richardhawthorn/piZero-Hub/images/image3.jpg

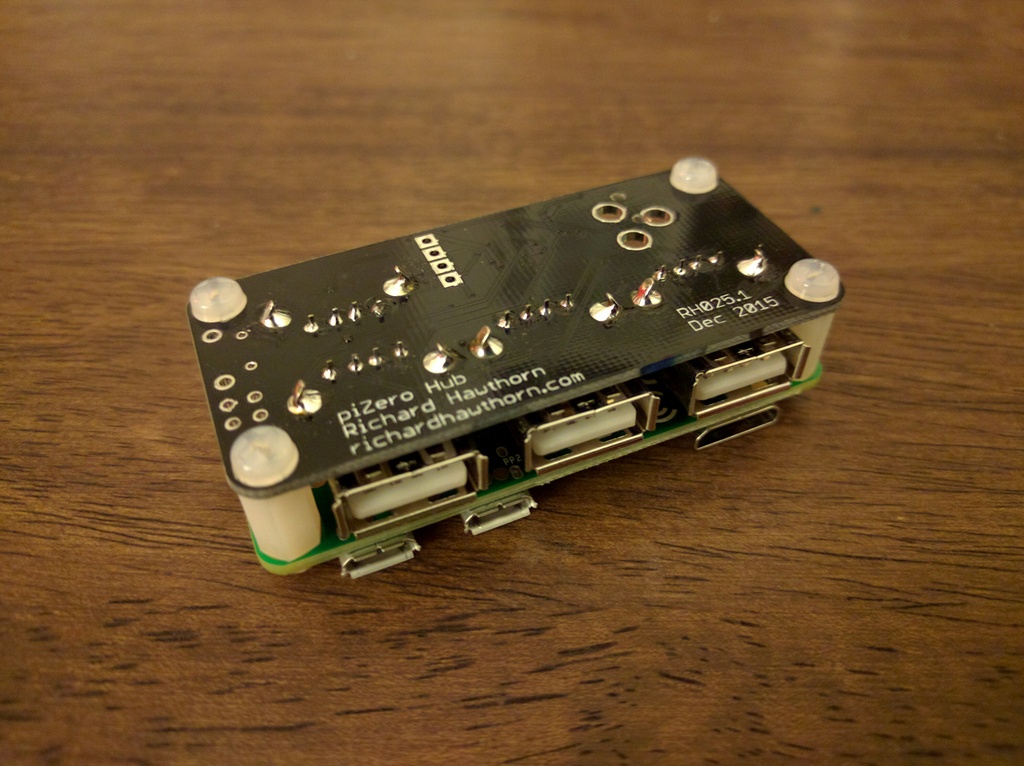
images/image3.jpg
