richardhawthorn/piZero-Hub/images/image4.jpg

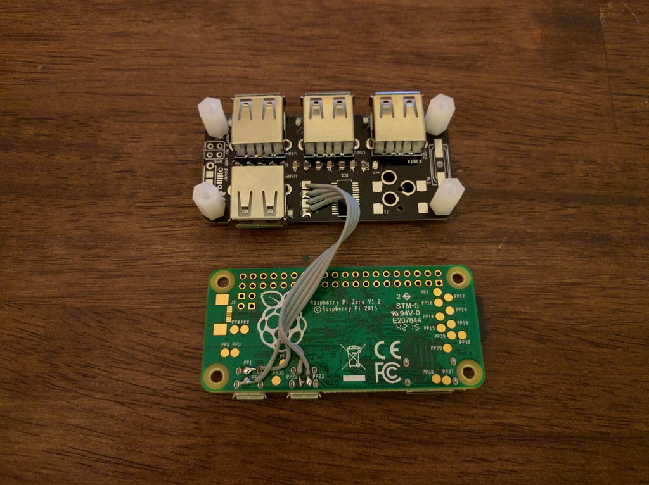
images/image4.jpg
