richardhawthorn/piZero-Hub/images/image6.jpg

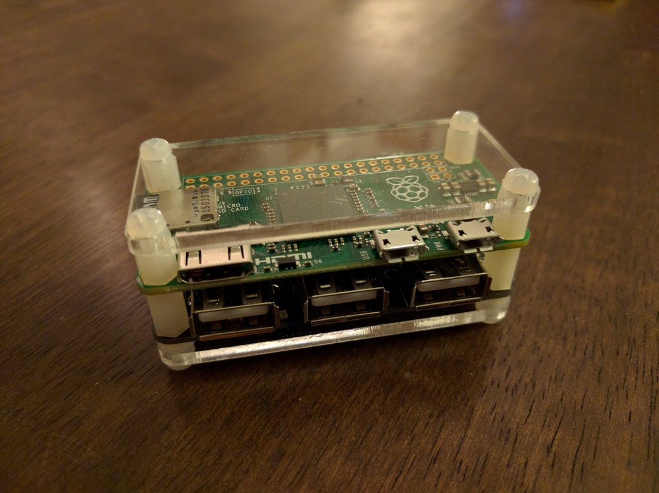
images/image6.jpg
